Jed0vcela/LED-matrix-Error-2026/dokumentace CZ/LED matrix error 2026.png

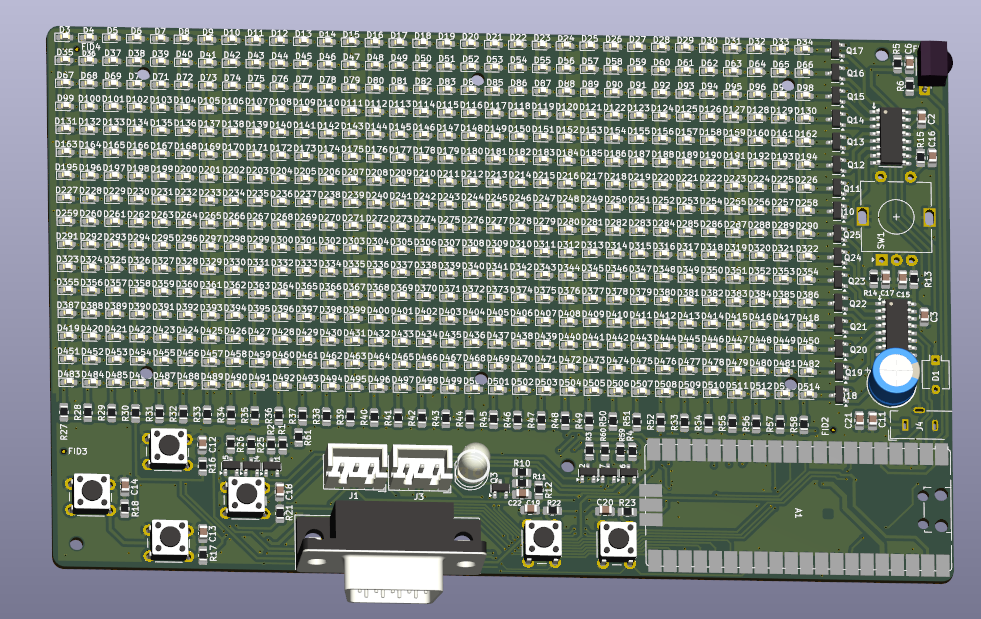
dokumentace CZ/LED matrix error 2026.png
