Jed0vcela/LED-matrix-Error-2026/navody, fotky/gamepad/image11.png

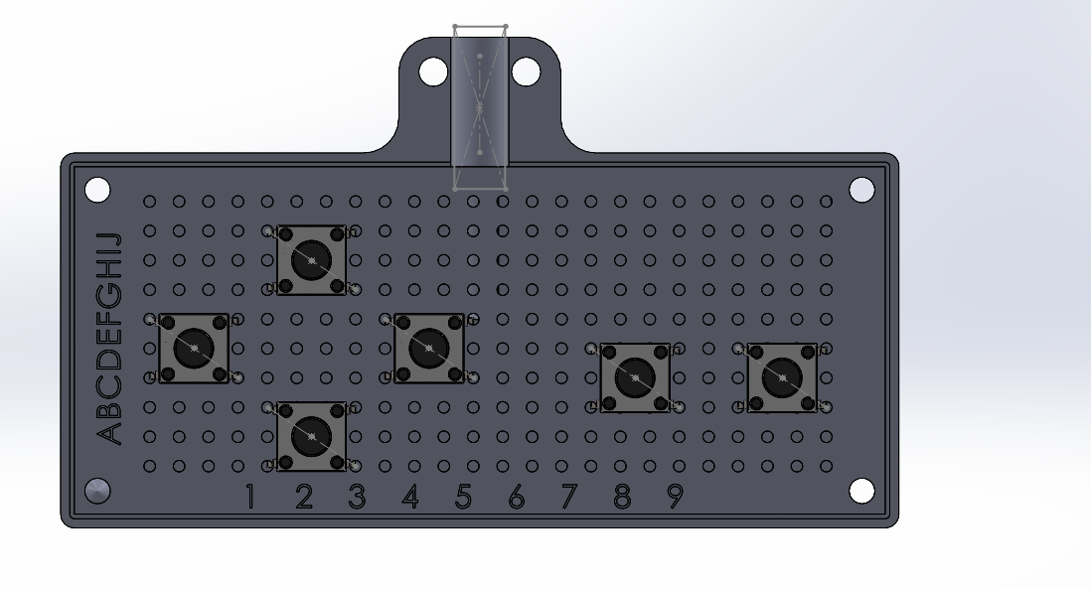
navody, fotky/gamepad/image11.png
