Jed0vcela/LED-matrix-Error-2026/navody, fotky/gamepad/image22.png

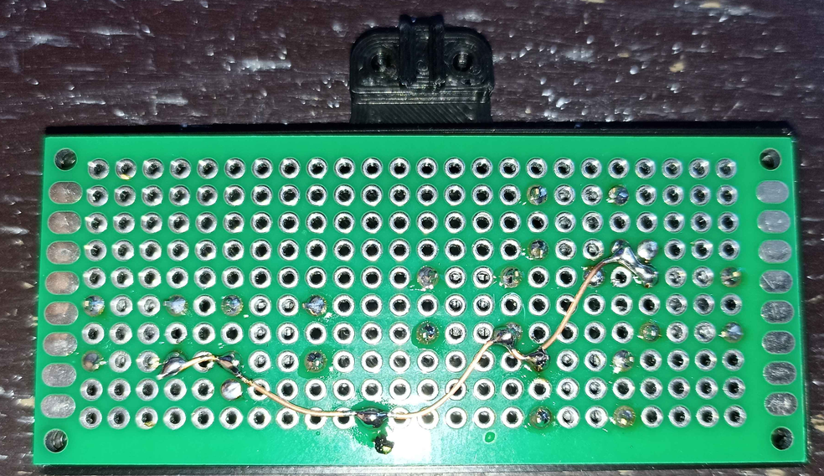
navody, fotky/gamepad/image22.png
