Jed0vcela/LED-matrix-Error-2026/navody, fotky/gamepad/image33.png

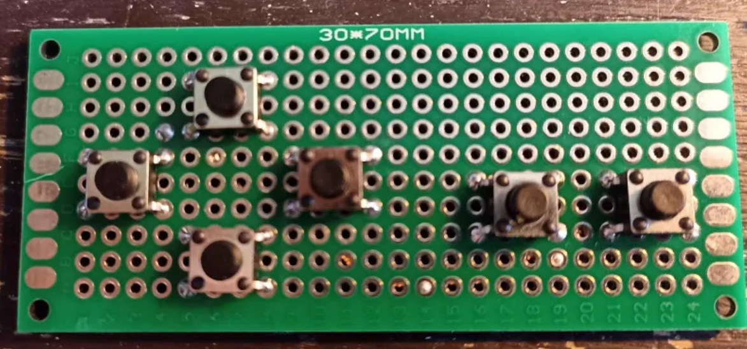
navody, fotky/gamepad/image33.png
