Jed0vcela/LED-matrix-Error-2026/navody, fotky/gamepad/image44.png

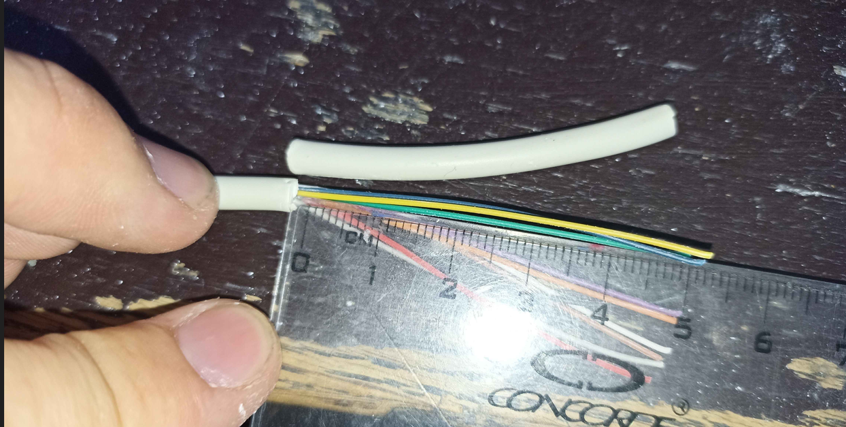
navody, fotky/gamepad/image44.png
