Jed0vcela/LED-matrix-Error-2026/navody, fotky/gamepad/image55.jpg

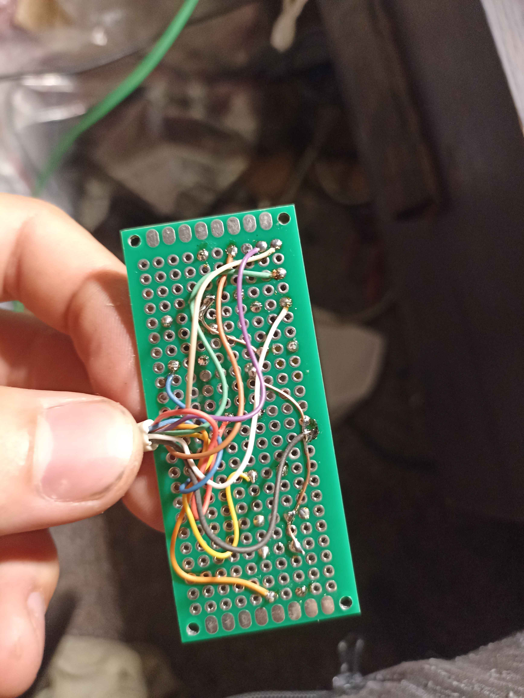
navody, fotky/gamepad/image55.jpg
