Jed0vcela/LED-matrix-Error-2026/navody, fotky/matrix/detail desky.jpg

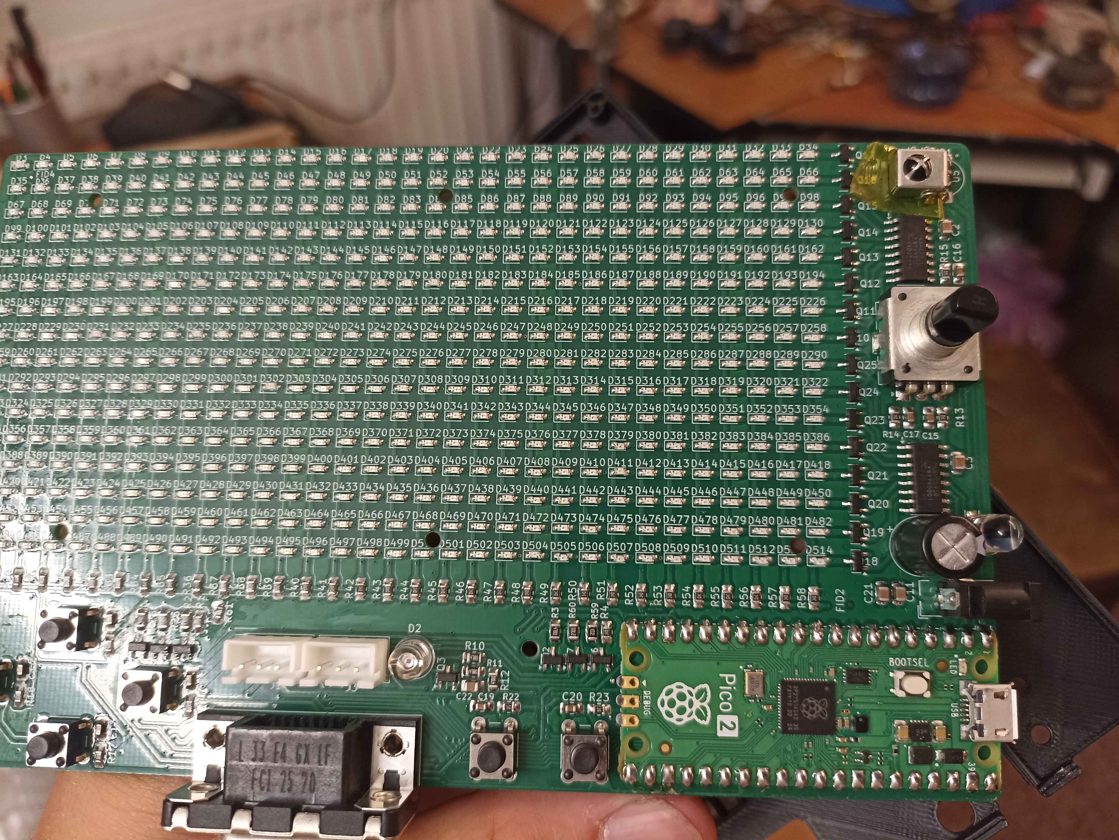
navody, fotky/matrix/detail desky.jpg
