Jed0vcela/LED-matrix-Error-2026/navody, fotky/matrix/drátování enkoderu0.jpg

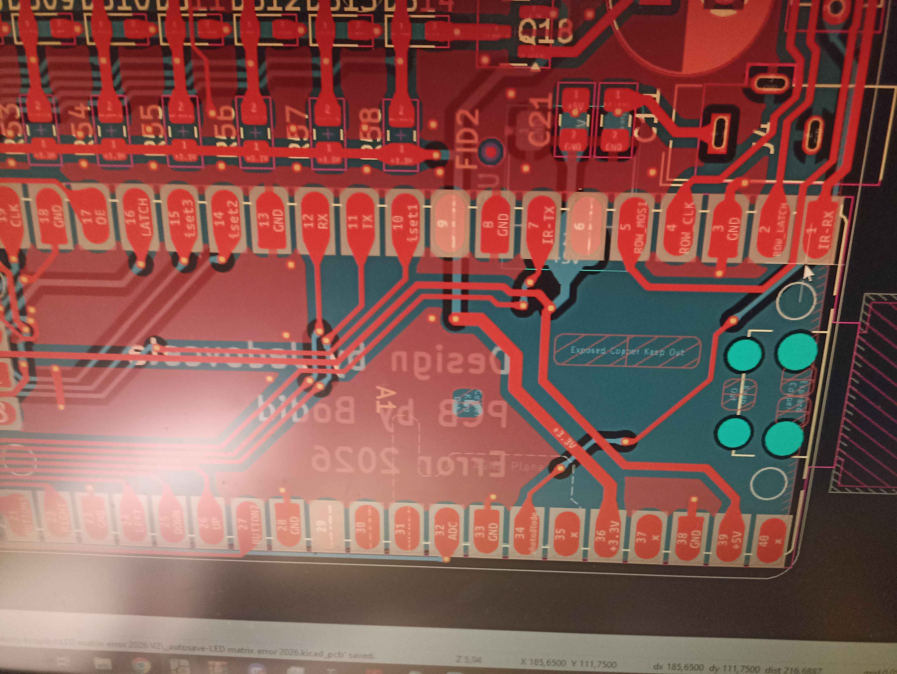
navody, fotky/matrix/drátování enkoderu0.jpg
