Jed0vcela/LED-matrix-Error-2026/navody, fotky/matrix/polarita fotodiody.jpg

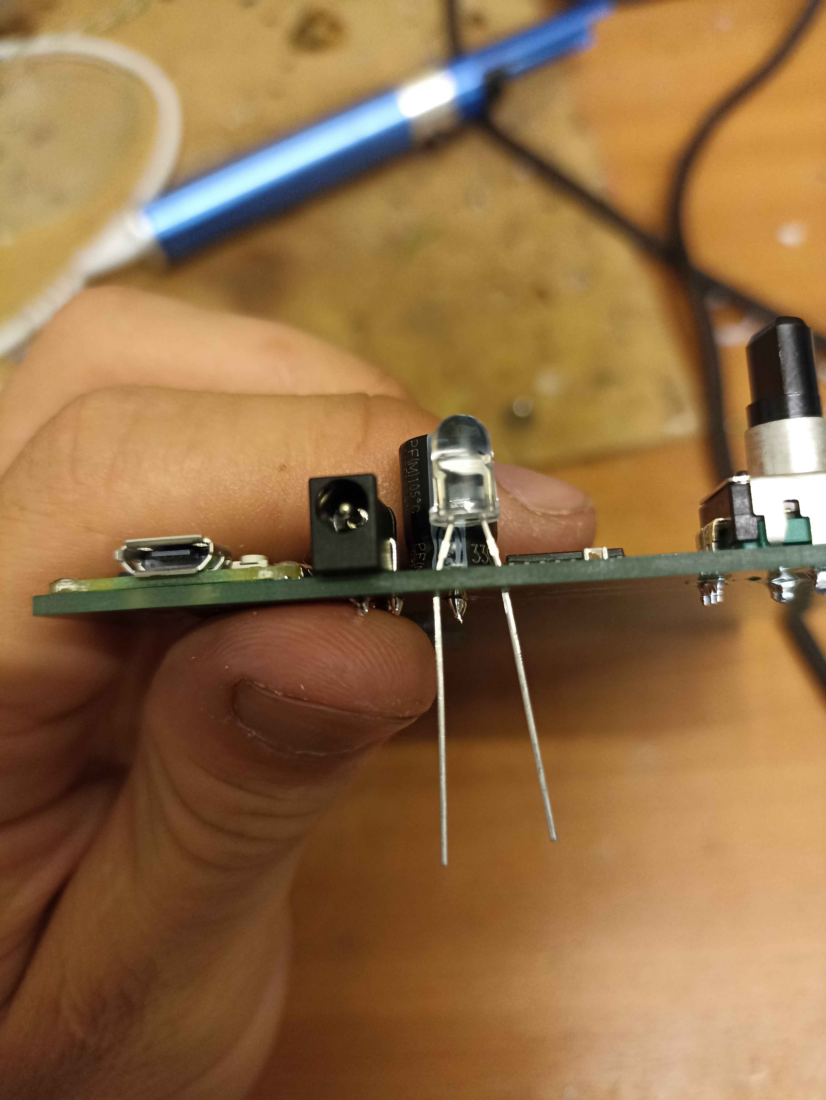
navody, fotky/matrix/polarita fotodiody.jpg
