Jed0vcela/LED-matrix-Error-2026/navody, fotky/matrix/polarita IR diody.jpg

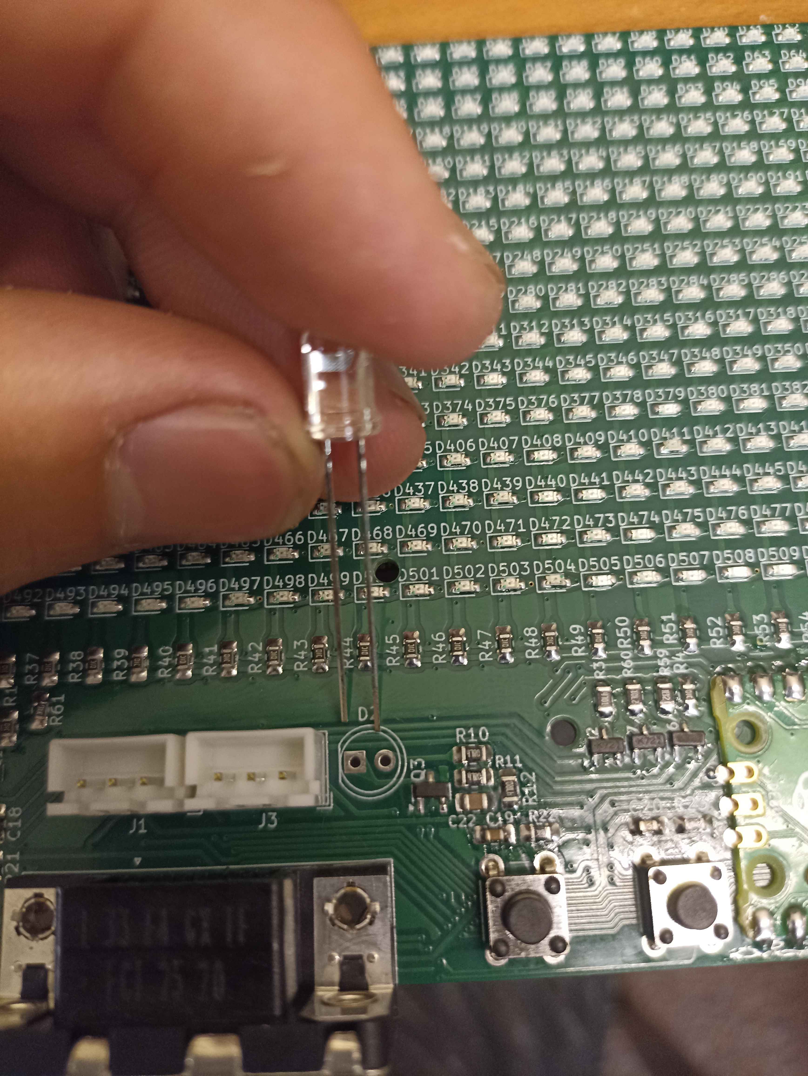
navody, fotky/matrix/polarita IR diody.jpg
