Jed0vcela/LED-matrix-Error-2026/3D files/gamepad/bottom^gamepad.STL

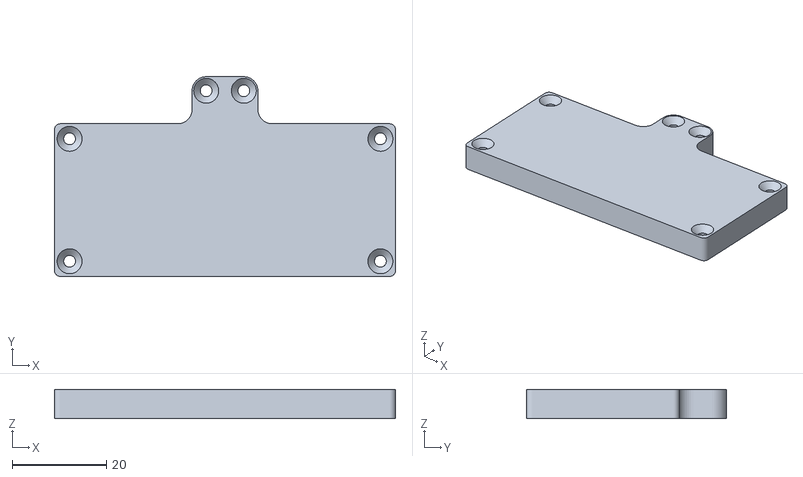
[picture p30: CAD file, 2026-07-20]
3D files/gamepad/bottom^gamepad.STL
72.4 x 42.4 x 6.20
