Jed0vcela/LED-matrix-Error-2026/3D files/enclosure/usb cable.SLDPRT

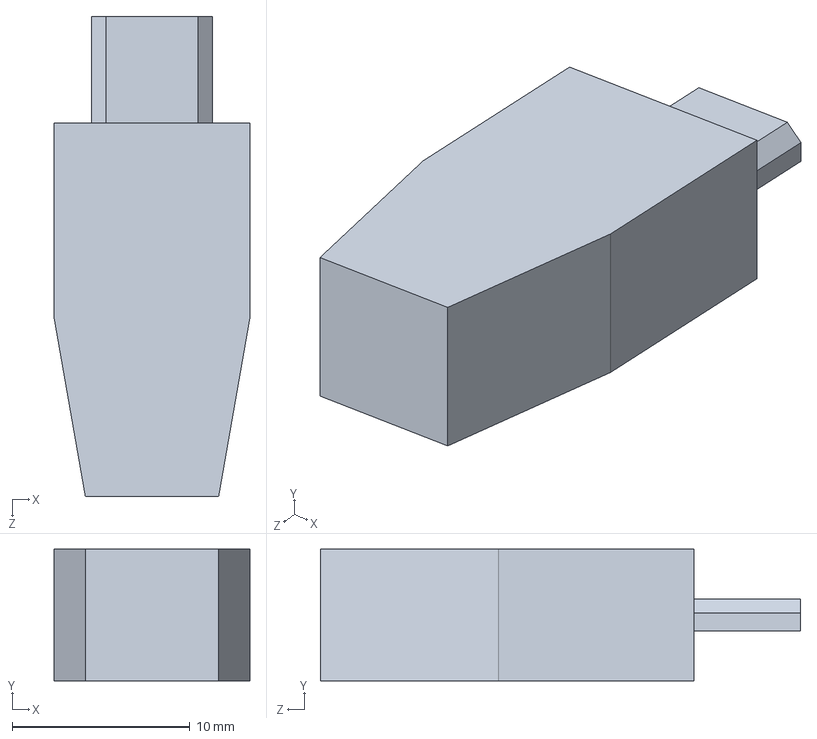
[picture p31: CAD file, 2026-07-20]
3D files/enclosure/usb cable.SLDPRT
11.0 x 7.40 x 27.0 mm
